platisd/indoor-navigation-system/server/src/data_store.cpp

//
// Created by samueli on 2017-10-10.
//

#include <sstream>

#include "data_store.hpp"

namespace ins_service
{

void DataStore::Init(const std::string& db_filename)
{
    console_->debug("+ DataStore::Init");

    int result = sqlite3_open(db_filename.c_str(), &database_);
    if (result != 0)
    {
        console_->error("Can't open database: {0}", sqlite3_errmsg(database_));
        return;
    }
    console_->info("Opened database successfully");
    if (!CreateLocationTable())
    {
        console_->error("Cannot create locations table");
    }

    console_->debug("- DataStore::Init");
    return;
}

void DataStore::Close()
{
    sqlite3_close(database_);
    database_ = nullptr;
}

bool DataStore::CreateLocationTable()
{
    console_->debug("+ DataStore::CreateLocationTable");

    std::string sql = "CREATE TABLE IF NOT EXISTS locations(device_id INTEGER PRIMARY KEY,"
                      "employee_id TEXT,"
                      "pos_x REAL,"
                      "pos_y REAL,"
                      "pos_z REAL,"
                      "timestamp datatime default current_timestamp);";
    console_->debug(sql);
    bool res = RunQuery(sql);

    console_->debug("- DataStore::CreateLocationTable");
    return res;
}

bool DataStore::CreateAccessPointTable()
{
    console_->debug("+ DataStore::CreateAccessPointTable");

    std::string sql = "CREATE TABLE IF NOT EXISTS access_points("
                      "mac_addr TEXT PRIMARY KEY,"
                      "pos_x REAL,"
                      "pos_y REAL,"
                      "pos_z REAL);";

    console_->debug(sql);
    bool res = RunQuery(sql);

    console_->debug("- DataStore::CreateAccessPointTable");
    return res;
}

bool DataStore::CreateDeviceTable(const std::string& device_id)
{
    console_->debug("+ DataStore::CreateDeviceTable");

    std::string sql = "CREATE TABLE IF NOT EXISTS dev_" + device_id + "(id INTEGER PRIMARY KEY,"
                                                                      "mac_addr TEXT, rssi REAL,"
                                                                      "timestamp datatime default current_timestamp);";
    console_->debug(sql);
    bool res = RunQuery(sql);

    console_->debug("- DataStore::CreateDeviceTable");
    return res;
}

bool DataStore::ClearDeviceTable(const std::string& device_id)
{
    console_->debug("+ DataStore::ClearDeviceTable");

    std::string sql = "DELETE from dev_" + device_id;
    console_->info(sql);
    bool res = RunQuery(sql);

    console_->debug("- DataStore::ClearDeviceTable");
    return res;
}

bool DataStore::UpdateDeviceLocation(const std::string& device_id, Position pos)
{
    console_->debug("+ DataStore::UpdateDeviceLocation");

    std::string sql = "INSERT OR REPLACE INTO locations (device_id, pos_x, pos_y, "
                      "pos_z, employee_id) VALUES ("
                      + device_id + "," + std::to_string(pos.x) + ", " + std::to_string(pos.y) + ", "
                      + std::to_string(pos.z) + ", (SELECT employee_id FROM locations WHERE device_id=" + device_id
                      + "));";
    console_->debug(sql);
    bool res = RunQuery(sql);

    console_->debug("- DataStore::UpdateDeviceLocation");
    return res;
}

bool DataStore::AssignDeviceToEmployee(const std::string& device_id, const std::string& employee_id)
{
    console_->debug("+ DataStore::AssignDeviceToEmployee");

    std::string sql = "INSERT OR REPLACE INTO locations (device_id, employee_id, pos_x, pos_y, pos_z) VALUES ("
                      + device_id + ",'" + employee_id + "',(SELECT pos_x FROM locations WHERE device_id=" + device_id
                      + "),(SELECT pos_y FROM locations WHERE device_id=" + device_id
                      + "),(SELECT pos_z FROM locations WHERE device_id=" + device_id + "));";
    console_->debug(sql);
    bool res = RunQuery(sql);

    console_->debug("- DataStore::AssignDeviceToEmployee");
    return res;
}

bool DataStore::InsertRSSIReadings(const std::string& device_id, std::vector<AccessPointRssiPair> accesspoint_rssi_list)
{
    console_->debug("+ DataStore::InsertRSSIReadings");

    // Construct multi-record insert sql
    std::stringstream sql;
    sql << "INSERT INTO ";
    sql << "dev_" << device_id << " (";
    sql << "mac_addr, rssi) ";
    sql << "VALUES";
    for (int i = 0; i < accesspoint_rssi_list.size(); ++i)
    {
        sql << "('" << accesspoint_rssi_list[i].first.mac_addr << "'," << accesspoint_rssi_list[i].second << ")";
        if (i < (accesspoint_rssi_list.size() - 1))
        {
            sql << ",";
        }
    }
    sql << ";";

    console_->debug(sql.str());
    bool res = RunQuery(sql.str());

    console_->debug("- DataStore::InsertRSSIReadings");
    return res;
}

bool DataStore::GetPosition(const std::string& id, QueryT query_by, Position& pos)
{
    console_->debug("+ DataStore::GetPosition");

    bool        result = false;
    std::string sql;

    if (query_by == QueryT::DEVICE)
        sql = "SELECT pos_x, pos_y, pos_z from locations WHERE device_id=" + id;
    else if (query_by == QueryT::EMPLOYEE)
        sql = "SELECT pos_x, pos_y, pos_z from locations WHERE employee_id='" + id + "'";
    else
    {
        console_->error("Invalid Query. Device or Employee is expected");
        return false;
    }
    sqlite3_stmt* selectStmt;
    sqlite3_prepare(database_, sql.c_str(), static_cast<int>(sql.length() + 1), &selectStmt, NULL);
    while (1)
    {
        int state = sqlite3_step(selectStmt);
        if (state == SQLITE_ROW)
        {
            pos.x  = sqlite3_column_double(selectStmt, 0);
            pos.y  = sqlite3_column_double(selectStmt, 1);
            pos.z  = sqlite3_column_double(selectStmt, 2);
            result = true;
        }
        else if (state == SQLITE_DONE)
        {
            break;
        }
        else
        {
            console_->error("Failed to read from database");
            sqlite3_finalize(selectStmt);
            return false;
        }
    }
    sqlite3_finalize(selectStmt);

    console_->debug("- DataStore::GetPosition");
    return result;
}

bool DataStore::RunQuery(const std::string& sql)
{
#ifdef ENABLE_TESTS
    executing_sql_ = sql;
#endif // ENABLE_TESTS

    std::lock_guard<std::mutex> guard(database_lock_);
    char*                       error_msg;
    auto                        result = sqlite3_exec(database_, sql.c_str(), DbCallback, 0, &error_msg);
    if (result != SQLITE_OK)
    {
        console_->error("SQL error: {0}", error_msg);
        sqlite3_free(error_msg);
        return false;
    }
    else
    {
        console_->info("SQL executed successfully");
        return true;
    }
}

int DataStore::DbCallback(void* not_used, int argc, char** argv, char** azColName)
{
    (void)not_used;
    auto logger = spdlog::get(LOGGER_NAME);
    if (logger == nullptr)
        logger = spdlog::stdout_logger_mt(LOGGER_NAME);
    logger->debug("+ DataStore::DbCallback");
    for (int i = 0; i < argc; i++)
    {
        logger->info("{0} = {1}", azColName[i], argv[i] ? argv[i] : "NULL");
    }
    logger->debug("- DataStore::DbCallback");
    return 0;
}

std::vector<AccessPoint> DataStore::GetDistinctAccessPoints(const std::string& device_id)
{
    console_->debug("+ DataStore::GetRSSIDataStream");

    std::vector<AccessPoint> access_points;
    std::string              sql = "SELECT DISTINCT mac_addr FROM dev_" + device_id + ";";

    sqlite3_stmt* selectStmt;
    sqlite3_prepare(database_, sql.c_str(), static_cast<int>(sql.length() + 1), &selectStmt, NULL);
    while (1)
    {
        int state = sqlite3_step(selectStmt);
        if (state == SQLITE_ROW)
        {
            AccessPoint ap(reinterpret_cast<const char*>(sqlite3_column_text(selectStmt, 0)));
            access_points.push_back(ap);

        }
        else if (state == SQLITE_DONE)
        {
            break;
        }
        else
        {
            console_->error("Failed to read from database");

            break;
        }
    }
    sqlite3_finalize(selectStmt);

    console_->debug("- DataStore::GetRSSIDataStream");
    return access_points;
}

std::vector<int32_t> DataStore::GetRSSISeriesFromDatabase(const std::string& device_id, AccessPoint access_point)
{
    console_->debug(" + DataStore::GetRSSISeriesDatabase");
    std::vector<int32_t> rssi_list;
    std::string          sql = "SELECT rssi FROM dev_" + device_id + " where mac_addr ='" + access_point.mac_addr + "';";
    sqlite3_stmt*        selectStmt;
    sqlite3_prepare(database_, sql.c_str(), static_cast<int>(sql.length() + 1), &selectStmt, NULL);

    while (1)
    {
        int state = sqlite3_step(selectStmt);
        if (state == SQLITE_ROW)
        {
            rssi_list.push_back(sqlite3_column_int(selectStmt, 0));
        }
        else if (state == SQLITE_DONE)
        {
            break;
        }
        else
        {
            console_->error("Failed to read from database");
            break;
        }
    }
    sqlite3_finalize(selectStmt);

    console_->debug(" - DataStore::GetRSSISeriesDatabase");
    return rssi_list;
}

std::vector<AccessPointRssiListPair> DataStore::GetRSSISeriesData(const std::string&       dev,
                                                              std::vector<AccessPoint> access_points)
{
    console_->debug("+ DataStore::GetRSSISeriesData");

    std::vector<AccessPointRssiListPair> accesspoint_rssi_list_pair;
    for (auto const& access_point : access_points)
    {
        accesspoint_rssi_list_pair.emplace_back(std::make_pair(access_point, GetRSSISeriesFromDatabase(dev, access_point)));
    }

    console_->debug("- DataStore::GetRSSISeriesData");
    return accesspoint_rssi_list_pair;
}

} // namespace ins_service
