platisd/indoor-navigation-system/ins-node/test/helpers/test_utils.h

#ifndef TEST_UTILS_H
#define TEST_UTILS_H

// ATtiny85 pinout according to https://github.com/SpenceKonde/ATTinyCore

enum ATTINY_PIN
{
    PB0,
    PB1,
    PB2,
    PB3,
    PB4
};

#endif
